IntergalacticMicrosystems/user_port_v9k/victor9k/src/device.h

/****************************************************************/
/*                                                              */
/*                           device.h                           */
/*                      Device Driver Header File               */
/*                                                              */
/*                       November 20, 1991                      */
/*                                                              */
/*                      Copyright (c) 1995                      */
/*                      Pasquale J. Villani                     */
/*                      All Rights Reserved                     */
/*                                                              */
/* This file is part of DOS-C.                                  */
/*                                                              */
/* DOS-C is free software; you can redistribute it and/or       */
/* modify it under the terms of the GNU General Public License  */
/* as published by the Free Software Foundation; either version */
/* 2, or (at your option) any later version.                    */
/*                                                              */
/* DOS-C is distributed in the hope that it will be useful, but */
/* WITHOUT ANY WARRANTY; without even the implied warranty of   */
/* MERCHANTABILITY or FITNESS FOR A PARTICULAR PURPOSE.  See    */
/* the GNU General Public License for more details.             */
/*                                                              */
/* You should have received a copy of the GNU General Public    */
/* License along with DOS-C; see the file COPYING.  If not,     */
/* write to the Free Software Foundation, 675 Mass Ave,         */
/* Cambridge, MA 02139, USA.                                    */
/****************************************************************/

/* Eduardo Casino: Slightly modified from the original:

    * define _DEVICE_H_ to avoid multiple inclusions

    * Use standard types

    * define C_MAXCMD

    * Add "_r_data" pointer to _r_par union in request struct and
      "r_data" to generic IOCTL macros
  
    * Define "MAX_SEC_SIZE" from dsk.h and remove the include

    * Remove references to kernel functions

*/

#ifndef _DEVICE_H_
#define _DEVICE_H_

#include <stdint.h>
#include <stdbool.h>

#include "../../common/protocols.h"

/*
 *      Status Word Bits
 */

#define S_ERROR         0x8000  /* Error bit                    */
#define S_BUSY          0x0200  /* Device busy bit              */
#define S_DONE          0x0100  /* Device operation completed   */
#define S_MASK          0x00ff  /* Mask to extract error code   */

/*
 *      MEDIA Descriptor Byte Bits
 */

#define MD_2SIDE        1       /* MEDIA is two sided           */
#define MD_8SECTOR      2       /* MEDIA is eight sectored      */
#define MD_REMOVABLE    4       /* MEDIA is removable (floppy)  */

/*
 *      Media Return Codes
 */
#define M_CHANGED       -1      /* MEDIA was changed            */
#define M_DONT_KNOW     0       /* MEDIA state unkown           */
#define M_NOT_CHANGED   1       /* MEDIA was not changed        */

/*
 *      Error Return Codes
 */

#define E_WRITE_PROTECT    0x00    /* Write Protect                */
#define E_UNKNOWN_UNIT     0x01    /* Unknown Unit                 */
#define E_NOT_READY        0x02    /* Device Not Ready             */
#define E_UNKNOWN_COMMAND  0x03    /* Unknown Command              */
#define E_CRC_ERROR        0x04    /* Crc Error                    */
#define E_HEADER_LENGTH    0x05    /* Bad Length                   */
#define E_SEEK_ERROR       0x06    /* Seek Error                   */
#define E_UNKNOWN_MEDIA    0x07    /* Unknown MEDIA                */
#define E_SECTOR_NOT_FND   0x08    /* Sector Not Found             */
#define E_NO_PAPER         0x09    /* No Paper                     */
#define E_WRITE_FAULT      0x0A    /* Write Fault                  */
#define E_READ_FAULT       0x0B    /* Read Fault                   */
#define E_GENERAL_FAILURE  0x0C    /* General Failure              */
#define E_MEDIA_CHANGED    0x0F    /* invalid diskette change      */

/*
 *      Command codes
 */

#define C_INIT          0x00    /* Initialize                   */
#define C_MEDIACHK      0x01    /* MEDIA Check                  */
#define C_BLDBPB        0x02    /* Build BPB                    */
#define C_IOCTLIN       0x03    /* Ioctl In                     */
#define C_INPUT         0x04    /* Input (Read)                 */
#define C_NDREAD        0x05    /* Non-destructive Read         */
#define C_ISTAT         0x06    /* Input Status                 */
#define C_IFLUSH        0x07    /* Input Flush                  */
#define C_OUTPUT        0x08    /* Output (Write)               */
#define C_OUTVFY        0x09    /* Output with verify           */
#define C_OSTAT         0x0a    /* Output                       */
#define C_OFLUSH        0x0b    /* Output Flush                 */
#define C_IOCTLOUT      0x0c    /* Ioctl Out                    */
#define C_OPEN          0x0d    /* Device Open                  */
#define C_CLOSE         0x0e    /* Device Close                 */
#define C_REMMEDIA      0x0f    /* Removable MEDIA              */
#define C_OUB           0x10    /* Output till busy             */
#define C_GENIOCTL      0x13    /* Generic Ioctl                */
#define C_GETLDEV       0x17    /* Get Logical Device           */
#define C_SETLDEV       0x18    /* Set Logical Device           */
#define C_IOCTLQRY      0x19    /* Ioctl Query                  */
#define C_MAXCMD        C_IOCTLQRY

/*
 * IOCTL Commands Victor 9K Specific
 */
#define GET_DISK_DRIVE_PHYSICAL_INFO 0x10

/*
 *      Convienence macros
 */
#define failure(x)      (S_ERROR+S_DONE+x)
#ifndef TRUE
#define TRUE            1
#endif
#ifndef FALSE
#define FALSE           0
#endif

/*
 *      structures
 */

#pragma pack(push, 1)

/* Device header */

struct device_header {
  struct device_header __far *dh_next;
  uint16_t dh_attr;
  void(near *dh_strategy) (void);
  void(near *dh_interrupt) (void);
  uint8_t dh_name[7];
};

#define ATTR_SUBST      0x8000
#define ATTR_CHAR       0x8000
#define ATTR_IOCTL      0x4000
#define ATTR_BLDFAT     0x2000
#define ATTR_REMOTE     0x1000
#define ATTR_EXCALLS    0x0800
#define ATTR_QRYIOCTL   0x0080
#define ATTR_GENIOCTL   0x0040
#define ATTR_RAW        0x0400
#define ATTR_FASTCON    0x0010
#define ATTR_CLOCK      0x0008
#define ATTR_NULL       0x0004
#define ATTR_CONOUT     0x0002
#define ATTR_HUGE       0x0002
#define ATTR_CONIN      0x0001

/*                                                                      */
/* Bios Parameter Block structure                                       */
/* Victor 9000 / Sirius 1 BIOS uses the following for the BPB, it's non-standard  */
/*                                                                      */
/* WORD bytes per sector                                                */
/* BYTE sectors per allocation unit (cluster)                           */
/* WORD number of reserved sectors                                      */
/* BYTE number of FATS                                                  */
/* WORD number of entries in the root directory                         */
/* WORD number of sectors in logical image of device                    */
/* BYTE media descriptor                                                */
/* WORD number of FAT sectors                                           */
/*                                                                      */
/* realized the above table was written when DOS x2.x was released. I'm going */
/* to assume the below table exists in Victor9K DOS 3.1.                */
/* http://www.bitsavers.org/pdf/victor/victor9000/Victor_9000_Systems_Programmers_Tool_Kit_II_Vol_II.pdf */
/*                                                                      */

#define FAT_NO_MIRRORING 0x80

#define BPB_SIZEOF 31           /* size of the standard BPB */


typedef struct {
  uint16_t bpb_nbyte;              /* Bytes per Sector             */
  uint8_t bpb_nsector;            /* Sectors per Allocation Unit  */
  uint16_t bpb_nreserved;          /* # Reserved Sectors           */
  uint8_t bpb_nfat;               /* # FATs                       */
  uint16_t bpb_ndirent;            /* # Root Directory entries     */
  uint16_t bpb_nsize;              /* Size in sectors              */ 
  uint8_t bpb_mdesc;              /* MEDIA Descriptor Byte        */
  uint16_t bpb_nfsect;             /* FAT size in sectors          */
  // uint16_t bpb_nsecs;              /* Sectors per track            */
  // uint16_t bpb_nheads;             /* Number of heads              */
  // uint32_t bpb_hidden;             /* Hidden sectors               */
  // uint32_t bpb_huge;               /* Size in sectors if           */
  /* bpb_nsize == 0               */
#ifdef WITHFAT32
  uint32_t bpb_xnfsect;            /* FAT size in sectors if       */
  /* bpb_nfsect == 0              */
  uint16_t bpb_xflags;             /* extended flags               */
  /* bit 7: disable mirroring     */
  /* bits 6-4: reserved (0)       */
  /* bits 3-0: active FAT number  */
  uint16_t bpb_xfsversion;         /* filesystem version           */
  uint32_t bpb_xrootclst;          /* starting cluster of root dir */
  uint16_t bpb_xfsinfosec;         /* FS info sector number,       */
  /* 0xFFFF if unknown            */
  uint16_t bpb_xbackupsec;         /* backup boot sector number    */
  /* 0xFFFF if unknown            */
#endif
} bpb;

#define N_RETRY         5       /* number of retries permitted  */

#ifndef MAX_SEC_SIZE
#define MAX_SEC_SIZE    (1*512) /* max supported size of sector in bytes */
#endif

#define LBA_READ         0x4200
#define LBA_WRITE        0x4300

struct _bios_LBA_address_packet
                                           /* Used to access a hard disk via LBA */
 /*       Added by Brian E. Reifsnyder */
{
  unsigned char packet_size;    /* size of this packet...set to 16  */
  unsigned char reserved_1;     /* set to 0...unused                */
  unsigned char number_of_blocks;       /* 0 < number_of_blocks < 128       */
  unsigned char reserved_2;     /* set to 0...unused                */
  uint8_t far *buffer_address;    /* addr of transfer buffer          */
  unsigned long block_address;  /* LBA address                      */
  unsigned long block_address_high;     /* high bytes of LBA addr...unused  */
};

struct CHS {
  uint16_t Cylinder;
  uint16_t Head;
  uint16_t Sector;
};

/* DOS 4.0-7.0 drive data table (see RBIL at INT2F,AX=0803) */
typedef struct ddtstruct {
  struct ddtstruct __far *ddt_next;
  /* pointer to next table (offset FFFFh if last table) */
  uint8_t ddt_driveno;            /* physical unit number (for INT 13)     */
  uint8_t ddt_logdriveno;         /* logical drive number (0=A:)        */
  bpb ddt_bpb;                  /* BIOS Parameter Block */
  uint8_t ddt_flags;
  /* bit 6: 16-bit FAT instead of 12-bit
     bit 7: unsupportable disk (all accesses will return Not Ready) */
  uint16_t ddt_FileOC;             /* Count of Open files on Drv */
  uint8_t ddt_type;               /* device type       */
  uint16_t ddt_descflags;          /* bit flags describing drive */
  uint16_t ddt_ncyl;               /* number of cylinders
                                   (for partition only, if hard disk) */
  bpb ddt_defbpb;               /* BPB for default (highest) capacity supported */
  uint8_t ddt_reserved[6];        /* (part of BPB above) */
  uint8_t ddt_ltrack;             /* last track accessed */
  union {
    uint32_t ddt_lasttime;         /* removable media: time of last access
                                   in clock ticks (FFFFFFFFh if never) */
    struct {
      uint16_t ddt_part;           /* partition (FFFFh = primary, 0001h = extended)
                                   always 0001h for DOS 5+ */
      uint16_t ddt_abscyl;         /* absolute cylinder number of partition's
                                   start on physical drive
                                   (FFFFh if primary partition in DOS 4.x) */
    } ddt_hd;
  } ddt_fh;
  uint8_t ddt_volume[12];         /* ASCIIZ volume label or "NO NAME    " if none
                                   (apparently taken from extended boot record
                                   rather than root directory) */
  uint32_t ddt_serialno;           /* serial number */
  uint8_t ddt_fstype[9];          /* ASCIIZ filesystem type ("FAT12   " or "FAT16   ") */
  uint32_t ddt_offset;             /* relative partition offset */
} ddt;

/* description flag bits */
#define DF_FIXED      0x001     /* fixed media, ie hard drive */
#define DF_CHANGELINE 0x002     /* door lock or disk change detection reported as supported */
#define DF_CURBPBLOCK 0x004     /* current BPB locked, use existing BPB instead of building one */
#define DF_SAMESIZE   0x008     /* all sectors in a track are the same size */
#define DF_MULTLOG    0x010     /* physical drive represents multiple logical ones, eg A: & B: */
#define DF_CURLOG     0x020     /* active (current) logical drive for this physical drive */
#define DF_DISKCHANGE 0x040     /* disk change was detected */
#define DF_DPCHANGED  0x080     /* device parameters changed */
#define DF_REFORMAT   0x100     /* disk formatted so BPB has changed */
#define DF_NOACCESS   0x200     /* don't allow access (read or write) to fixed media */
/* freedos specific flag bits */
#define DF_LBA        0x400
#define DF_WRTVERIFY  0x800
#define DF_DMA_TRANSPARENT   0x1000 /* DMA boundary errors are handled transparently */

/* typedef struct ddtstruct ddt;*/

struct gblkio {
  uint8_t gbio_spcfunbit;
  uint8_t gbio_devtype;
  uint16_t gbio_devattrib;
  uint16_t gbio_ncyl;
  uint8_t gbio_media;
  bpb gbio_bpb;
  uint16_t gbio_nsecs;
};

struct gblkfv                   /* for format / verify track */
{
  uint8_t gbfv_spcfunbit;
  uint16_t gbfv_head;
  uint16_t gbfv_cyl;
  uint16_t gbfv_ntracks;
};

struct gblkrw                   /* for read / write track */
{
  uint8_t gbrw_spcfunbit;
  uint16_t gbrw_head;
  uint16_t gbrw_cyl;
  uint16_t gbrw_sector;
  uint16_t gbrw_nsecs;
  uint8_t __far *gbrw_buffer;
};

struct Gioc_media {
  int16_t ioc_level;
  uint32_t ioc_serialno;
  int8_t ioc_volume[11];
  int8_t ioc_fstype[8];
};

struct Access_info {
  int8_t AI_spec;
  int8_t AI_Flag;
};

/*                                                                      */
/* Boot Block (Super Block)                                             */
/*                                                                      */
/* See BPB comments for the offsets below                               */
/*                                                                      */
#define BT_JUMP         0
#define BT_OEM          3
#define BT_BPB          11
#define BT_SIZEOF       36

typedef struct {
  int8_t bt_jump[3];              /* Boot Jump opcodes            */
  int8_t bt_oem[8];               /* OEM Name                     */
  bpb bt_bpb;                   /* BPB for this media/device    */
  int16_t bt_nsecs;                /* # Sectors per Track          */
  int16_t bt_nheads;               /* # Heads                      */
  int16_t bt_hidden;               /* # Hidden sectors             */
  int32_t bt_huge;                 /* use if nsecs == 0            */
  int8_t bt_drvno;
  int8_t bt_reserv;
  int8_t bt_btid;
  uint32_t bt_serialno;
  int8_t bt_volume[11];
  int8_t bt_fstype[8];
} boot;

/* File system information structure */
struct fsinfo {
  uint32_t fi_signature;          /* must be 0x61417272 */
  int32_t fi_nfreeclst;           /* number of free clusters, -1 if unknown */
  int32_t fi_cluster;             /* most recently allocated cluster, -1 if unknown */
  uint8_t fi_reserved[12];
};

/* Victor 9000 IOCTL Get_Disk_Drive_Physical_Info() data structure */
typedef struct {
  uint8_t di_ioctl_type;     /* Get_Disk_Drive_Physical_Info() always 0x10h. */
  uint8_t di_ioctl_status;   /* 0 if successful, 1 if error */
  uint8_t di_disk_type;       /* 0 = floppy. 1 = hard drive */
  uint8_t di_disk_location;   /* for floppy only 0 = left, 1 = right drive */
} V9kDiskInfo;

typedef boot super;             /* Alias for boot structure             */

typedef bpb *near bpb_tbl_t[MAX_IMG_FILES];     /*  Array of near pointers to BPBs    */

typedef struct {
  uint8_t r_length;               /*  Request Header length               */
  uint8_t r_unit;                 /*  Unit Code                           */
  uint8_t r_command;              /*  Command Code                        */
  uint16_t r_status;              /*  Status                              */
  int8_t r_reserved[8];           /*  DOS Reserved Area                   */
  union {
    struct {
      uint8_t _r_nunits;          /*  number of units     */
      int8_t __far *_r_endaddr;   /*  Ending Address      */
      bpb_tbl_t far * _r_bpb_tbl_ptr;     /*  ptr to BPB array    */
      uint8_t _r_firstunit;
    } _r_init;
    struct {
      int8_t _r_media_desc;       /*  MEDIA Descriptor    */
      int8_t _r_ret_code;         /*  Return Code         */
    } _r_media;
    struct {
      int8_t _r_meddesc;          /*  MEDIA Descriptor    */
      boot __far * _r_fat;        /*  boot sector pointer */
      bpb __far * _r_bpb_ptr;           /*  ptr to BPB table    */
    } _r_bpb;
    struct {
      int8_t _r_media_desc;       /*  MEDIA Descriptor    */
      int8_t far *_r_trans;       /*  Transfer Address    */
      uint16_t _r_count;          /*  Byte/Sector Count   */
      uint16_t _r_start;          /*  Starting Sector No. */
    } _r_rw;
    struct {
      unsigned char _r_ndbyte;  /*  Byte Read From Device       */
    } _r_nd;
    struct {
      uint8_t _r_cat;             /* Category code */
      uint8_t _r_fun;             /* Function code */
      uint16_t _r_si;              /* Contents of SI and DI */
      uint16_t _r_di;              /* (PC DOS 7 Technical Update, pp 104,105) */
      union
      {
        struct gblkio __far *_r_io;
        struct gblkrw __far *_r_rw;
        struct gblkfv __far *_r_fv;
        struct Gioc_media __far *_r_gioc;
        struct Access_info __far *_r_ai;
        void __far *_r_data;
      } _r_par;                 /* Pointer to param. block from 440C/440D */
    } _r_gen;
  } _r_x;
} request;

#define HUGECOUNT       0xffff
#define MAXSHORT        0xffffl

/*
 * Macros to assist request structure legibility
 */

/* Init packet macros                                                   */
#define r_nunits        _r_x._r_init._r_nunits
#define r_endaddr       _r_x._r_init._r_endaddr
#define r_bpb_tbl_ptr        _r_x._r_init._r_bpb_tbl_ptr
#define r_firstunit     _r_x._r_init._r_firstunit

/* MEDIA Check packet macros                                            */
#define r_media_check   _r_x._r_media
#define r_mc_media_desc _r_x._r_media._r_media_desc
#define r_mc_ret_code   _r_x._r_media._r_ret_code

/* Build BPB packet macros                                              */
#define r_bpmdesc       _r_x._r_bpb._r_meddesc
#define r_bpfat         _r_x._r_bpb._r_fat
#define r_bpb_ptr         _r_x._r_bpb._r_bpb_ptr

/* rw packet macros                                                     */
#define r_rw_ptr        _r_x._r_rw
#define r_meddesc       _r_x._r_rw._r_media_desc
#define r_trans         _r_x._r_rw._r_trans
#define r_count         _r_x._r_rw._r_count
#define r_start         _r_x._r_rw._r_start

/* ndread packet macros                                                 */
#define r_ndbyte        _r_x._r_nd._r_ndbyte

/* generic IOCTL and IOCTL query macros */
#define r_cat           _r_x._r_gen._r_cat
#define r_fun           _r_x._r_gen._r_fun
#define r_si            _r_x._r_gen._r_si
#define r_di            _r_x._r_gen._r_di
#define r_rw            _r_x._r_gen._r_par._r_rw
#define r_io            _r_x._r_gen._r_par._r_io
#define r_fv            _r_x._r_gen._r_par._r_fv
#define r_gioc          _r_x._r_gen._r_par._r_gioc
#define r_ai            _r_x._r_gen._r_par._r_ai
#define r_data          _r_x._r_gen._r_par._r_data


/*
 *interrupt support (spl & splx) support - IBM style
 */

#define I_NONE          0       /* Initial value                        */

/* predefined interrupt levels - 8259 support                           */
#define IRQ0            0x01    /* Level 0 - highest                    */
#define IRQ1            0x02
#define IRQ2            0x04
#define IRQ3            0x08
#define IRQ4            0x10
#define IRQ5            0x20
#define IRQ6            0x40
#define IRQ7            0x80    /* Level 7 - lowest             */

/* standard hardware configuration                                      */
#define I_RTC           IRQ0    /* Timer                        */
#define I_KBD           IRQ1    /* Keyboard                     */
#define I_COM2          IRQ3    /* COM1:                        */
#define I_COM1          IRQ4    /* COM2:                        */
#define I_HDC           IRQ5    /* Fixed disk                   */
#define I_FDC           IRQ6    /* Diskette                     */
#define I_PRT           IRQ7    /* Printer                      */

/* standard hardware vectors - 8259 defined                             */
#define V_RTC           0x08    /* Timer                        */
#define V_KBD           0x09    /* Keyboard                     */
#define V_LEV2          0x0a    /* Level 2 - uncomitted         */
#define V_COM2          0x0b    /* COM1:                        */
#define V_COM1          0x0c    /* COM2:                        */
#define V_HDC           0x0d    /* Fixed disk                   */
#define V_FDC           0x0e    /* Diskette                     */
#define V_PRT           0x0f    /* Printer                      */

#define V_LEV0          0x08    /* Level 0 - highest            */
#define V_LEV1          0x09
#define V_LEV2          0x0a    /* Level 2 - uncomitted         */
#define V_LEV3          0x0b
#define V_LEV4          0x0c
#define V_LEV5          0x0d
#define V_LEV6          0x0e
#define V_LEV7          0x0f    /* Level 7 - lowest             */

/*
 */
typedef request __far *rqptr;
typedef int8_t __far *byteptr;
typedef struct dhdr __far *dhdrptr;

#pragma pack( pop )

static bool parse_options (char far *);

#define SECTOR_SIZE 512                         // sector size in bytes

#undef RAMDRIVE 


#ifdef RAMDRIVE
#define MAX_RAM_DISK_SIZE_KB 768
#define MAX_SECTORS_POSSIBLE (MAX_RAM_DISK_SIZE_KB * 1024 / SECTOR_SIZE) //768KB * 1024 / 512 = 1536
#define MAX_SEGMENTS (MAX_RAM_DISK_SIZE_KB / 64) //64KB segments allocatable by DOS

#define NUM_SECTORS 32 

typedef struct {
    uint8_t data[SECTOR_SIZE];
} Sector;

typedef struct {
    Sector sectors[NUM_SECTORS];
} MiniDrive;
#endif /* RAMDRIVE */

#endif /* _DEVICE_H_ */
/*
 *      end of device.h
 */
