IntergalacticMicrosystems/user_port_v9k/pico/pico_communication.c

#include <stdio.h>
#include <stdlib.h>
#include <stdbool.h>

#include "pico/stdlib.h"
#include "hardware/clocks.h"
#include "hardware/pio.h"
#include "pico/multicore.h"
#include "receive_fifo.pio.h"
#include "transmit_fifo.pio.h"

#include "../common/protocols.h"
#include "../common/crc8.h"
#include "pico_communication.h"
#include "command_dispatch.h"
#include "sd_block_device.h"

PIO_state* init_pio(void) {
    stdio_init_all();

    printf("pico booting up pack!\n");
    const uint LED_PIN = 25;
    gpio_init(LED_PIN);
    gpio_set_dir(LED_PIN, GPIO_OUT);

    gpio_put(LED_PIN, 1);
    sleep_ms(250);
    gpio_put(LED_PIN, 0);
    sleep_ms(250);
    gpio_put(LED_PIN, 1);
    sleep_ms(250);
    gpio_put(LED_PIN, 0);
    sleep_ms(10);
 
    PIO_state *pio_state;
    pio_state->pio = pio0;
    pio_state->rx_sm = pio_claim_unused_sm(pio_state->pio, true);
    pio_state->tx_sm = pio_claim_unused_sm(pio_state->pio, true);

    if (pio_state->rx_sm == -1) {
        printf("Error: Failed to claim a state machine for RX\n");
        pio_state->tx_sm = -1;
        return pio_state;;  // or handle error appropriately
    }

    if (pio_state->tx_sm == -1) {
        printf("Error: Failed to claim a state machine for TX\n");
        return pio_state;;  // or handle error appropriately
    }

    uint tx_offset = pio_add_program(pio_state->pio, &transmit_fifo_program);
    if (tx_offset == -1) {
        printf("Error: Failed to load transmit FIFO program\n");
        return pio_state;
    }

    uint rx_offset = pio_add_program(pio_state->pio, &receive_fifo_program);
    if (rx_offset == -1) {
        printf("Error: Failed to load receive FIFO program\n");
        return pio_state;
    }

    const uint RX_DATA_READY = 22;
    gpio_init(RX_DATA_READY);
    gpio_set_dir(RX_DATA_READY, GPIO_IN);

    const uint RX_TAKEN_PIN = 28;
    gpio_init(RX_TAKEN_PIN);
    gpio_set_dir(RX_TAKEN_PIN, GPIO_OUT);
    gpio_put(RX_TAKEN_PIN, 1);

    // clear RX state machine
    pio_sm_set_enabled(pio_state->pio, pio_state->rx_sm, false);
    pio_sm_clear_fifos(pio_state->pio, pio_state->rx_sm);
    pio_sm_restart(pio_state->pio, pio_state->rx_sm);

    // clear TX state machine
    pio_sm_set_enabled(pio_state->pio, pio_state->tx_sm, false);
    pio_sm_clear_fifos(pio_state->pio, pio_state->tx_sm);
    pio_sm_restart(pio_state->pio, pio_state->tx_sm);

    //for 1 MHz signal, sample PIO at 4MHz for clarity of signal
    //float target_freq = 4.0e6;  // 4MHz in Hz
    float target_freq = 4.0e6; 
    //equal to 125MHz system clock / 4MHz sampling rate
    float clkdiv = clock_get_hz(clk_sys) / target_freq; 

    printf("clock divider: %2.2f\n", clkdiv);

    printf("pico initing PIO\n");
    receive_fifo_init(pio_state->pio, pio_state->rx_sm, rx_offset, clkdiv);
    transmit_fifo_init(pio_state->pio, pio_state->tx_sm, tx_offset, clkdiv);
    return pio_state;
}

void process_incoming_commands(SDState *sd_state, PIO_state *pio_state) {
    while (true) {
        Payload *payload = (Payload*)malloc(sizeof(Payload));
        if (payload == NULL) {
            printf("Error: Memory allocation failed for payload\n");
            return;
        }

        payload->cmd = (VictorCommand *)malloc(sizeof(VictorCommand));
        if (payload->cmd == NULL) {
            printf("Error: Memory allocation failed for command\n");
            free(payload);
            return;
        }

        payload->data = (Data *)malloc(sizeof(Data));
        if (payload->data == NULL) {
            printf("Error: Memory allocation failed for data\n");
            free(payload->cmd);
            free(payload);
            return;
        }

        receive_command_payload(pio_state, payload);
        bool success = dispatchCommand(sd_state, pio_state, payload);
        if (!success) {
            printf("Error: Command dispatch failed\n");
        }
        free(payload->data->buffer);
        free(payload->data);
        free(payload->cmd->params);
        free(payload->cmd);
        free(payload);
    }
}

void receive_command_payload(PIO_state *pio_state, Payload *payload) {
    
    receive_command(pio_state, payload->cmd);
    while (crc8_check_command(payload->cmd) ) {
        pio_sm_put_blocking(pio_state->pio, pio_state->tx_sm, false);  //send a CRC failure Response
        receive_command(pio_state, payload->cmd);    
    }
    pio_sm_put_blocking(pio_state->pio, pio_state->tx_sm, true);  //send a CRC success Response

    
    receive_data(pio_state, payload->data);
    while ( crc8_check_data(payload->data) ) {
        pio_sm_put_blocking(pio_state->pio, pio_state->tx_sm, false);  //send a CRC failure Response
        receive_data(pio_state, payload->data);
    }
    pio_sm_put_blocking(pio_state->pio, pio_state->tx_sm, true);  //send a CRC success Response
}

void receive_command(PIO_state *pio_state, VictorCommand *cmd) {
    cmd->protocol = (V9KProtocol) pio_sm_get_blocking(pio_state->pio, pio_state->rx_sm);
    cmd->byte_count = pio_sm_get_blocking(pio_state->pio, pio_state->rx_sm);
    cmd->command = pio_sm_get_blocking(pio_state->pio, pio_state->rx_sm);
    cmd->params = malloc(cmd->byte_count);
    if (cmd->params == NULL) {
        printf("Error: Memory allocation failed for cmd params\n");
        return;
    }
    for(int i = 0; i < cmd->byte_count; ++i) {
        cmd->params[i] = pio_sm_get_blocking(pio_state->pio, pio_state->rx_sm);
    }
    cmd->expected_crc = pio_sm_get_blocking(pio_state->pio, pio_state->rx_sm);
}

void receive_data(PIO_state *pio_state, Data *data) {
    uint8_t high_byte = pio_sm_get_blocking(pio_state->pio, pio_state->rx_sm);
    uint8_t low_byte = pio_sm_get_blocking(pio_state->pio, pio_state->rx_sm);
    data->byte_count = (high_byte << 8) | low_byte;
    
    data->buffer = malloc(data->byte_count);
    if (data->buffer == NULL) {
        printf("Error: Memory allocation failed for cmd_params buffer\n");
        return;
    }
    for(int i = 0; i < data->byte_count; ++i) {
        data->buffer[i] = pio_sm_get_blocking(pio_state->pio, pio_state->rx_sm);
    }
    data->expected_crc = pio_sm_get_blocking(pio_state->pio, pio_state->rx_sm);
}
